makethingshappy/IoTextra-Analog/Analog3/v.3.11/media/IoTextra Analog3 BOTTOM view.png

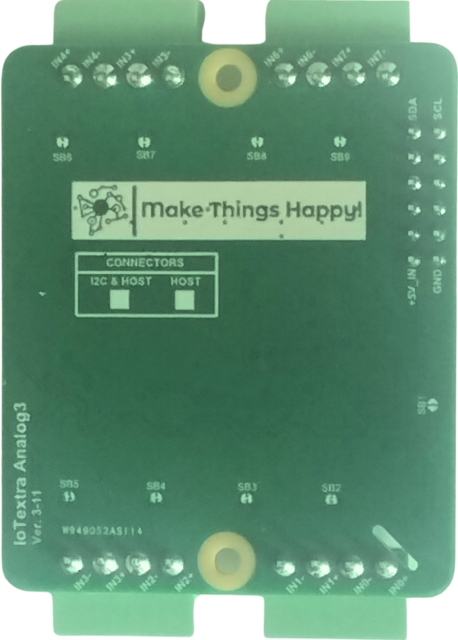
Analog3/v.3.11/media/IoTextra Analog3 BOTTOM view.png
