makethingshappy/IoTextra-Analog/Analog3/v.3.11/media/IoTextra Analog3 HOST.png

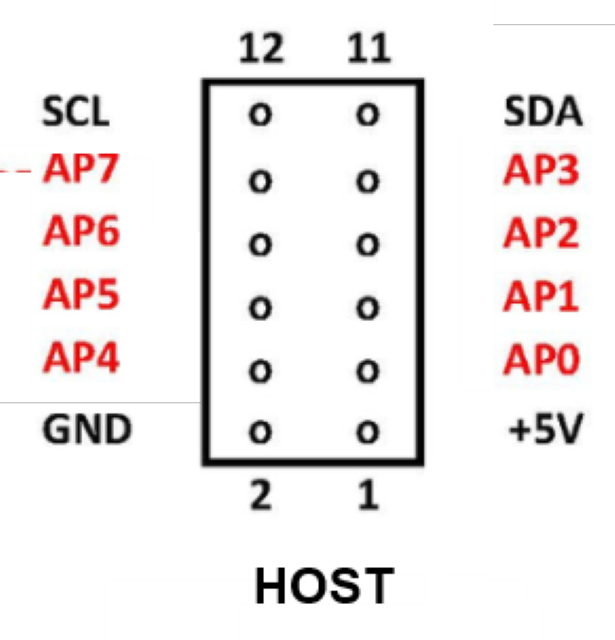
Analog3/v.3.11/media/IoTextra Analog3 HOST.png
