makethingshappy/IoTextra-Analog/Analog3/v.3.11/media/IoTextra Analog3 with IoTbase Feather and Particle Photon2.png

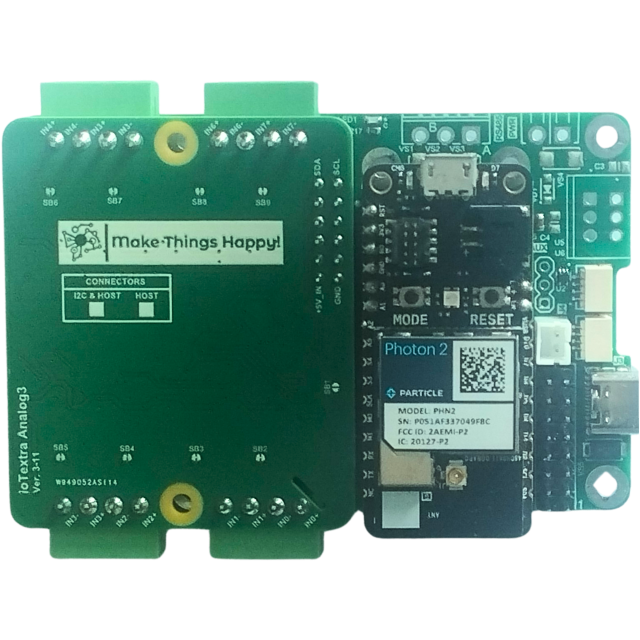
Analog3/v.3.11/media/IoTextra Analog3 with IoTbase Feather and Particle Photon2.png
