makethingshappy/IoTextra-Analog/Analog3/v.3.11/media/IoTextra Analog3 with IoTbase NANO and Waveshare ESP32-S3-Nano.png

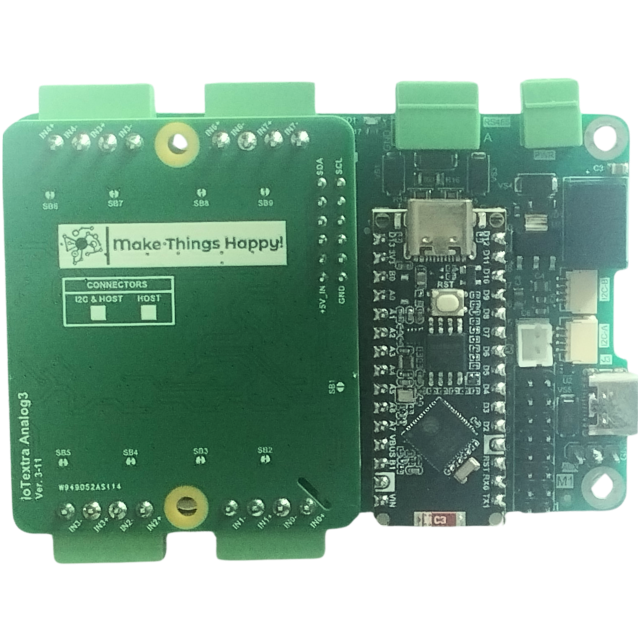
Analog3/v.3.11/media/IoTextra Analog3 with IoTbase NANO and Waveshare ESP32-S3-Nano.png
