makethingshappy/IoTextra-Analog/Analog3/v.3.11/media/IoTextra Analog3 with IoTbase PICO and Waveshare ESP32-S3-Pico.png

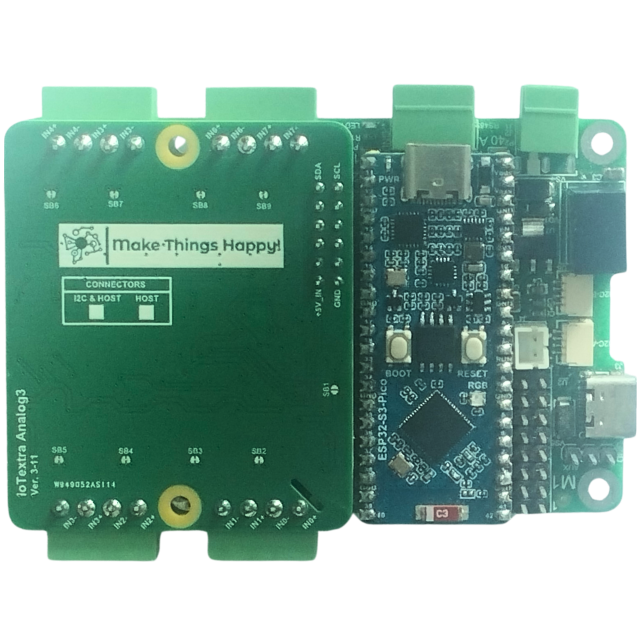
Analog3/v.3.11/media/IoTextra Analog3 with IoTbase PICO and Waveshare ESP32-S3-Pico.png
