makethingshappy/IoTextra-Analog/Analog3/v.3.11/media/IoTextra Analog3 with IoTsmart ESP32-S3.png

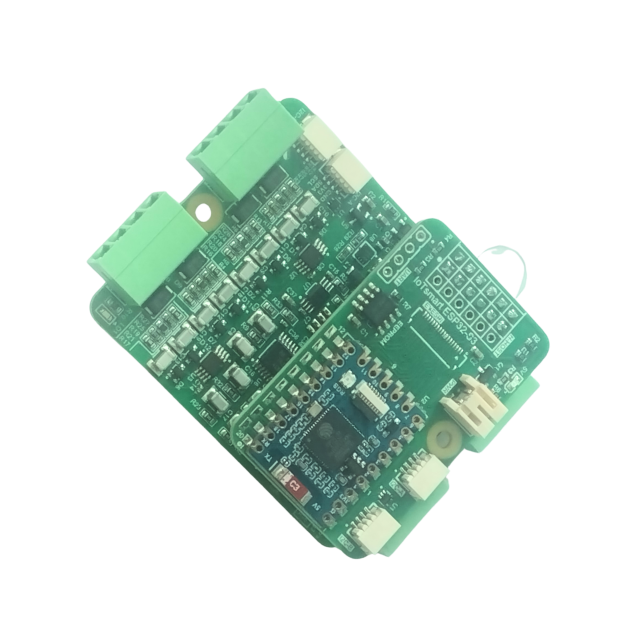
Analog3/v.3.11/media/IoTextra Analog3 with IoTsmart ESP32-S3.png
