makethingshappy/IoTextra-Analog/Analog3/v.3.11/media/IoTextra Analog3 with IoTsmart RP2040.png

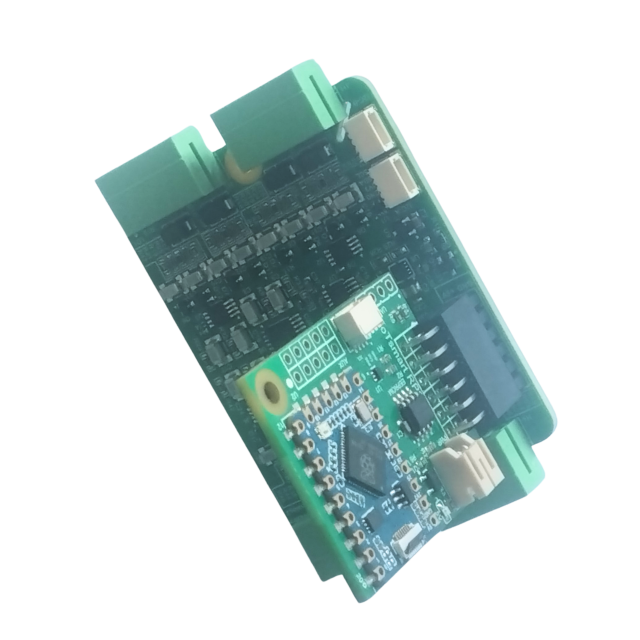
Analog3/v.3.11/media/IoTextra Analog3 with IoTsmart RP2040.png
