makethingshappy/IoTextra-Analog/Analog3/v.3.11/media/IoTextra Analog3 with IoTsmart XIAO and XIAO ESP32-C6.png

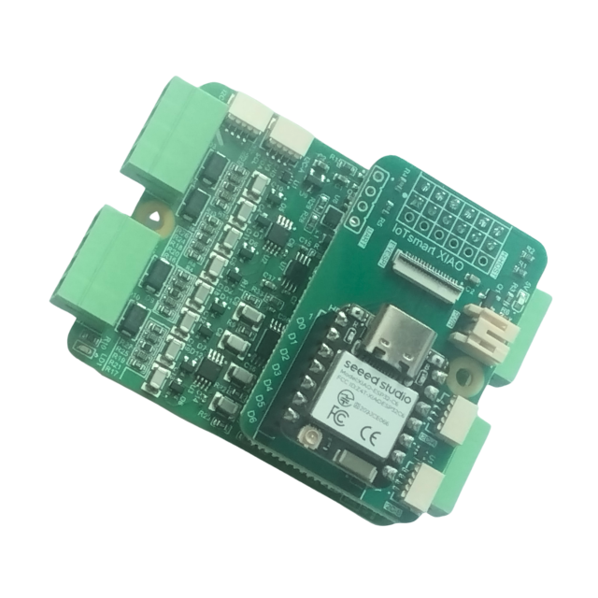
Analog3/v.3.11/media/IoTextra Analog3 with IoTsmart XIAO and XIAO ESP32-C6.png
