makethingshappy/IoTextra-Analog/Analog/v.3.12/media/01A - IoTextra Analog 3-12 - 3D view - 2.png

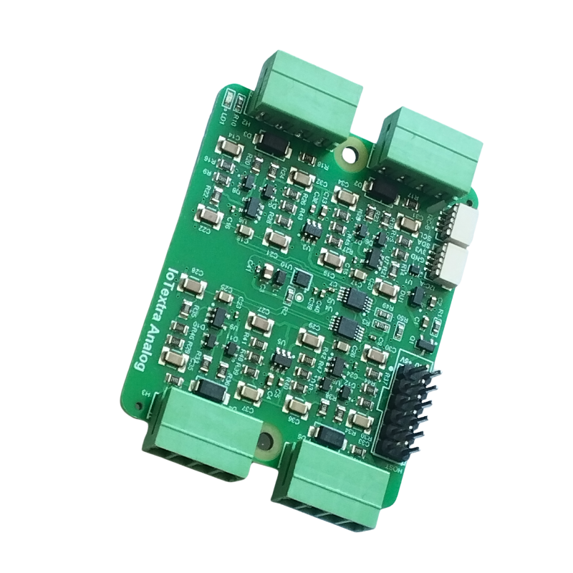
Analog/v.3.12/media/01A - IoTextra Analog 3-12 - 3D view - 2.png
