makethingshappy/IoTextra-Analog/Analog/v.3.12/media/01B - IoTextra Analog 3-12 - 3D view - 3.png

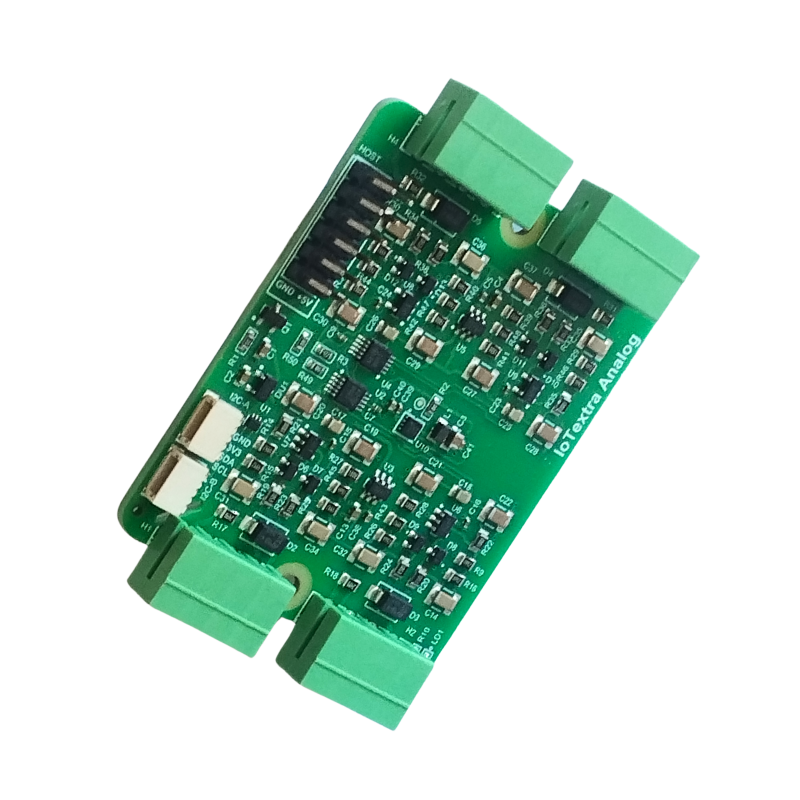
Analog/v.3.12/media/01B - IoTextra Analog 3-12 - 3D view - 3.png
