makethingshappy/IoTextra-Analog/Analog/v.3.12/media/03 - IoTextra Analog 3-12 - BOTTOM view - 1.png

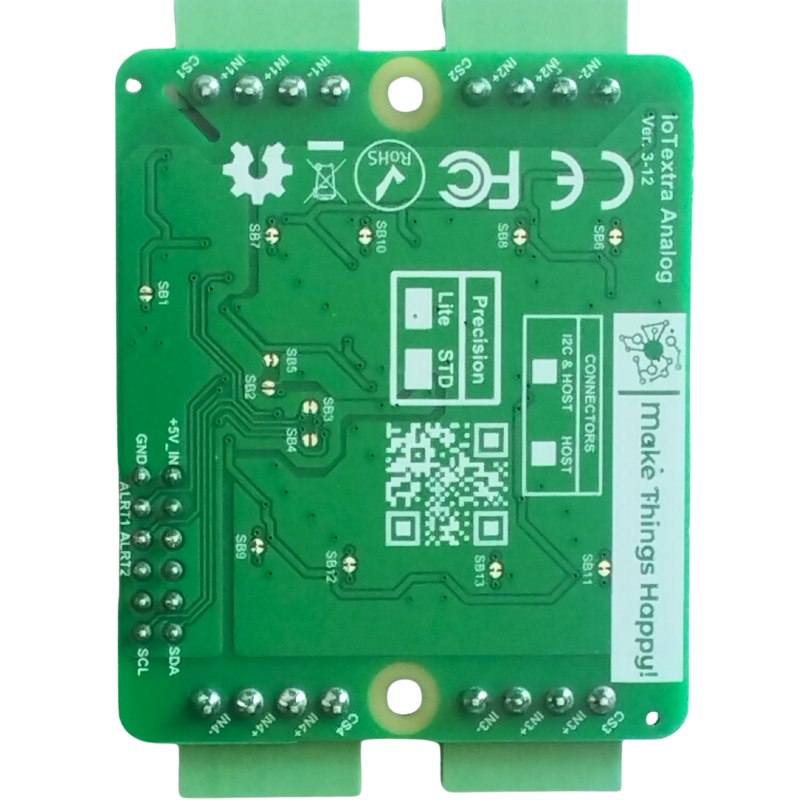
Analog/v.3.12/media/03 - IoTextra Analog 3-12 - BOTTOM view - 1.png
