makethingshappy/IoTextra-Analog/Analog/v.3.12/media/05 - IoTextra Analog 3-12 and IoTsmart RP2040 - 2.png

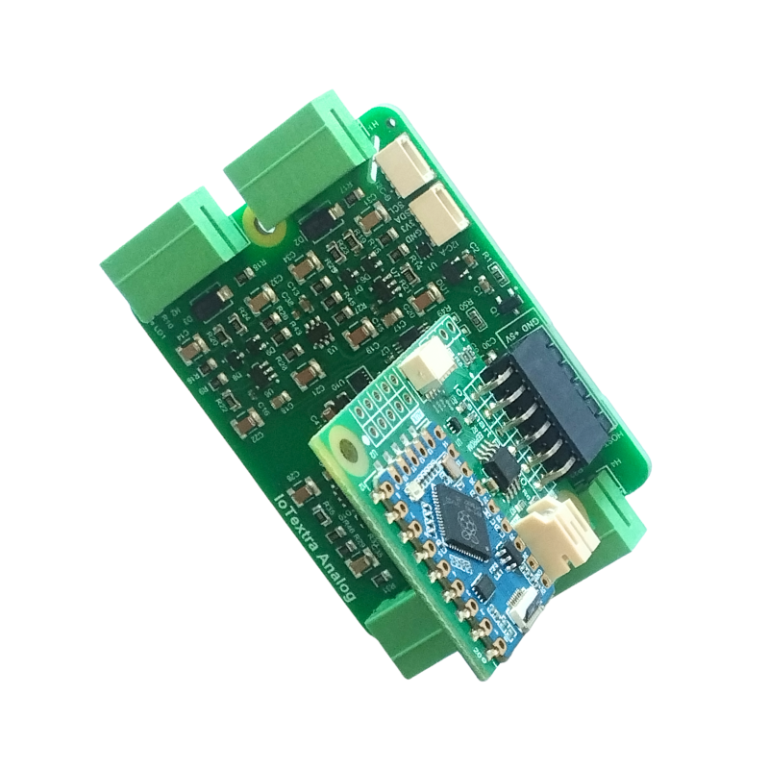
Analog/v.3.12/media/05 - IoTextra Analog 3-12 and IoTsmart RP2040 - 2.png
