makethingshappy/IoTextra-Analog/Analog/v.3.12/media/07- IoTextra Analog 3-12 and IoTsmart ESP32-S3 - 1.png

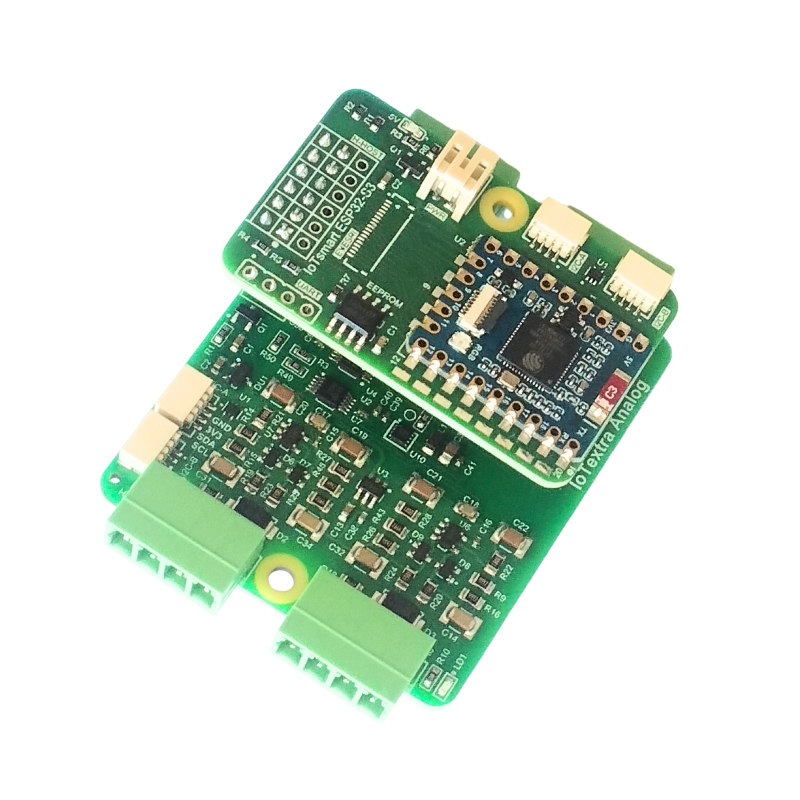
Analog/v.3.12/media/07- IoTextra Analog 3-12 and IoTsmart ESP32-S3 - 1.png
