makethingshappy/IoTextra-Analog/Analog/v.3.12/media/10 - IoTextra Analog 3-12 and IoTbase PICO with PICO2.png

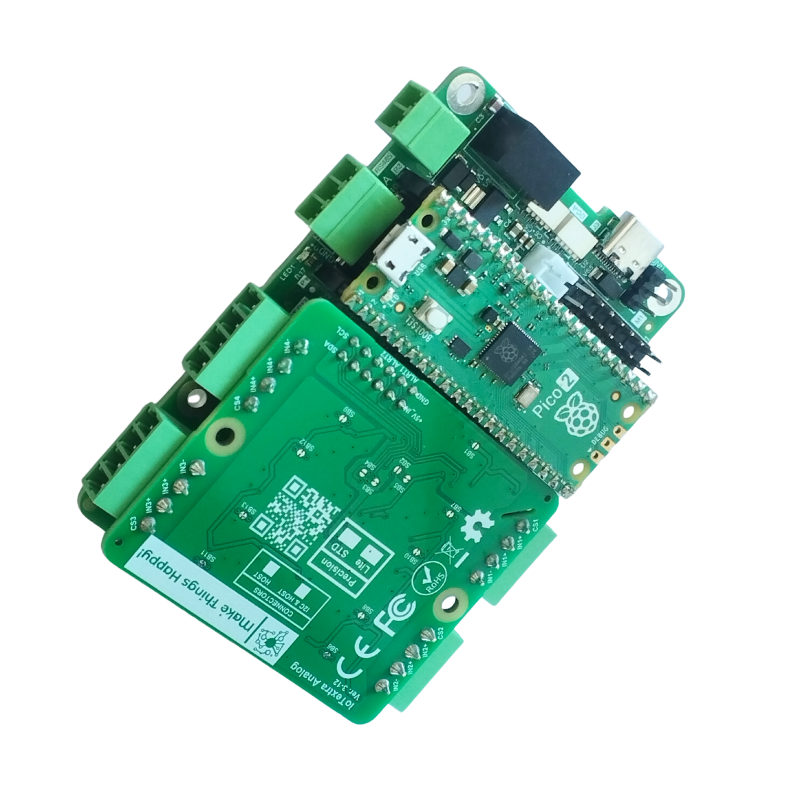
Analog/v.3.12/media/10 - IoTextra Analog 3-12 and IoTbase PICO with PICO2.png
