makethingshappy/IoTextra-Analog/Analog/v.3.12/media/12 - IoTextra Analog 3-12 and IoTbase NANO with Waveshare ESP32-S3 Nano.png

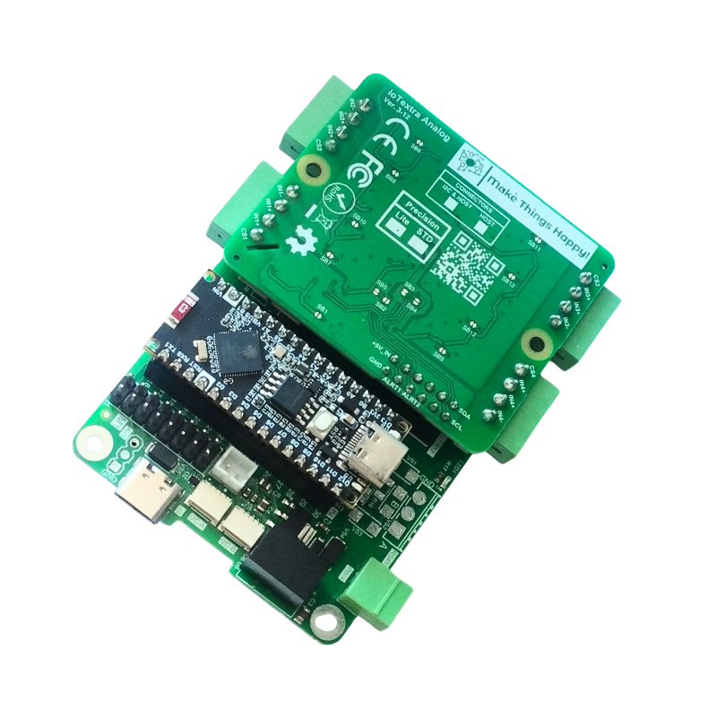
Analog/v.3.12/media/12 - IoTextra Analog 3-12 and IoTbase NANO with Waveshare ESP32-S3 Nano.png
