makethingshappy/IoTextra-Analog/Analog/v.3.12/media/13 - IoTextra Analog 3-12 and IoTbase NANO with Nucleo-32.png

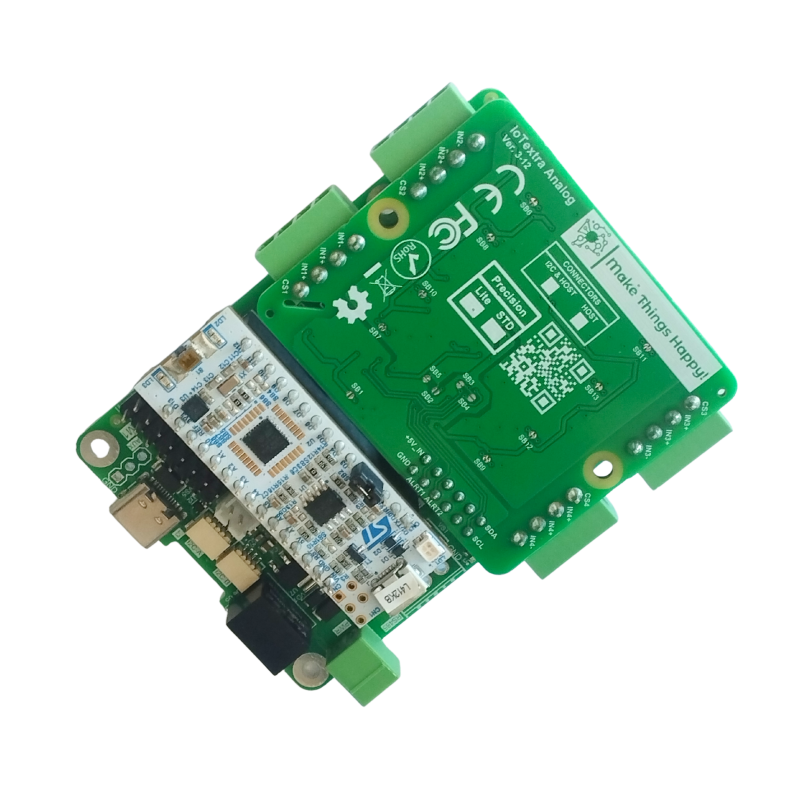
Analog/v.3.12/media/13 - IoTextra Analog 3-12 and IoTbase NANO with Nucleo-32.png
